likeablob/mini-media-control-bar/kicad/mmcb.kicad_sch

## KiCad design kicad/mmcb.kicad_sch (2025-04-27)

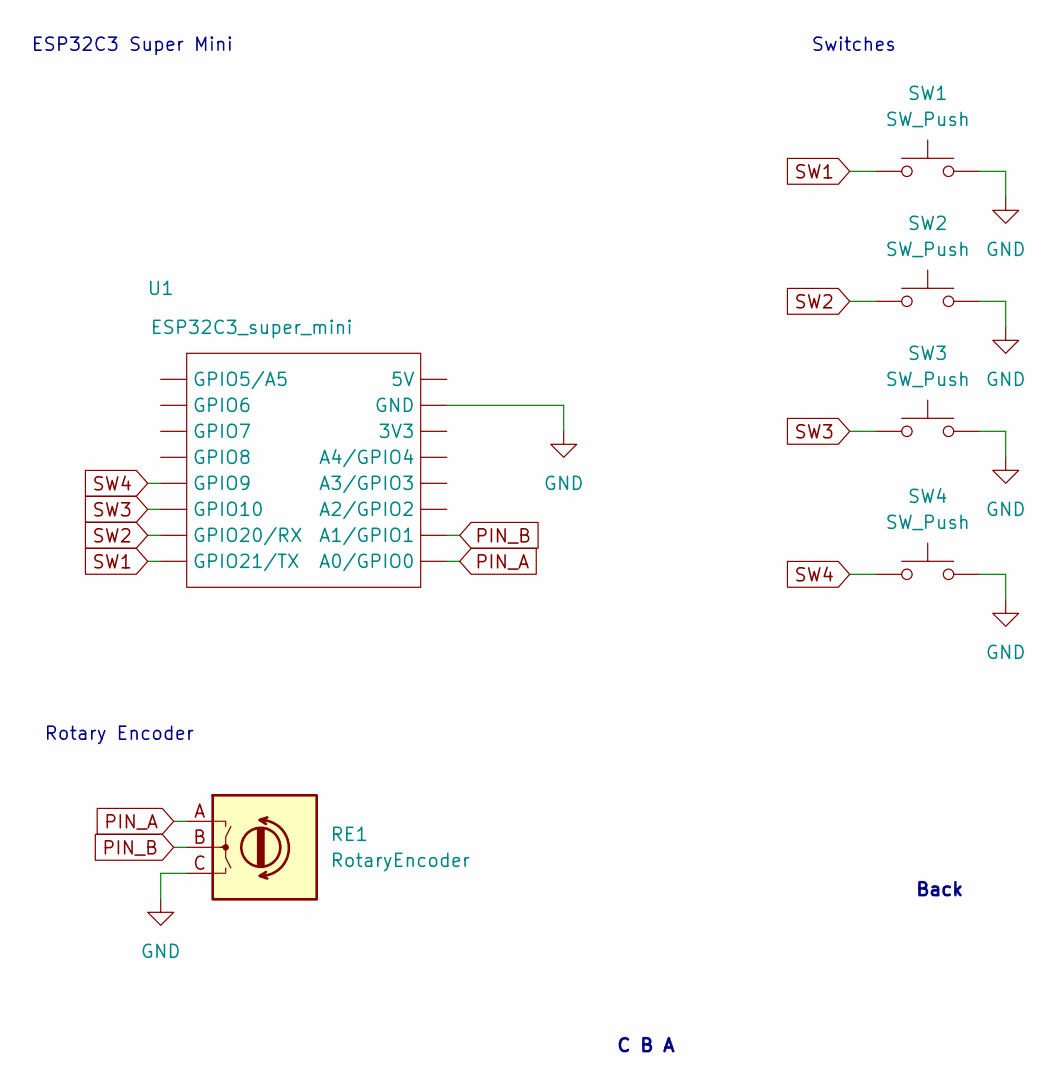
[picture p11: schematic mmcb.kicad_sch]

Parts:
RE1: RotaryEncoder
SW1, SW2, SW3, SW4: SW_Push
U1: ESP32C3_super_mini

Connections:
GND: RE1.C, SW1.2, SW2.2, SW3.2, SW4.2
PIN_A: RE1.A, U1.
PIN_B: RE1.B, U1.
SW1: SW1.1, U1.
SW2: SW2.1, U1.
SW3: SW3.1, U1.
SW4: SW4.1, U1.

Notes on the sheet:
Rotary Encoder
ESP32C3 Super Mini
C B A
Switches
Back
